SagiK-Repository/Balancer/docs/motor_test/test_1/motor_test_3_1749901958.csv

Time | Target0 | Target1 | Actual0 | Actual1 | Roll | Pitch | Confidence | Pos0 | Pos1
0.0002 | 10.0000 | 0.0000 | 14.9983 | -15.7754 | 0.0000 | 0.0000 | 0.0000 | 0.0012 | -0.0012
0.0200 | 10.0000 | 0.0000 | 14.9983 | -15.7754 | 0.0000 | 0.0000 | 0.0000 | 0.1001 | -0.1053
0.0411 | 10.0000 | 0.0000 | 14.9983 | -15.7754 | 0.0000 | 0.0000 | 0.0000 | 0.2057 | -0.2163
0.0611 | 10.0000 | 0.0000 | 14.9983 | -15.7754 | 0.0000 | 0.0000 | 0.0000 | 0.3054 | -0.3212
0.0811 | 10.0000 | 0.0000 | 14.9983 | -15.7754 | 0.0000 | 0.0000 | 0.0000 | 0.4054 | -0.4264
0.1011 | 10.0000 | 0.0000 | 14.9983 | -15.7754 | 0.0000 | 0.0000 | 0.0000 | 0.5054 | -0.5316
0.1211 | 10.0000 | 0.0000 | 14.9983 | -0.6457 | 0.0000 | 0.0000 | 0.0000 | 0.6054 | -0.0261
0.1413 | 10.0000 | 0.0000 | 14.9983 | -0.6457 | 0.0000 | 0.0000 | 0.0000 | 0.7067 | -0.0304
0.1611 | 10.0000 | 0.0000 | 14.9983 | -0.6457 | 0.0000 | 0.0000 | 0.0000 | 0.8053 | -0.0347
0.1811 | 10.0000 | 0.0000 | 14.9983 | -0.6457 | 0.0000 | 0.0000 | 0.0000 | 0.9053 | -0.0390
0.2011 | 10.0000 | 0.0000 | 14.9983 | -0.6457 | 0.0000 | 0.0000 | 0.0000 | 1.0052 | -0.0433
0.2211 | 10.0000 | 0.0000 | 14.9983 | -205.9349 | 0.0000 | 0.0000 | 0.0000 | 1.1053 | -15.1758
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
