SagiK-Repository/Balancer/docs/motor_test/test_1/motor_test_4_1749901995.csv

Time | Target0 | Target1 | Actual0 | Actual1 | Roll | Pitch | Confidence | Pos0 | Pos1
0.0001 | 1.0000 | 0.0000 | 14.9983 | 265.8498 | 0.0000 | 0.0000 | 0.0000 | 0.0005 | 0.0096
0.0206 | 1.0000 | 0.0000 | 14.9983 | 265.8498 | 0.0000 | 0.0000 | 0.0000 | 0.1032 | 1.8298
0.0411 | 1.0000 | 0.0000 | 14.9983 | 265.8498 | 0.0000 | 0.0000 | 0.0000 | 0.2054 | 3.6415
0.0611 | 1.0000 | 0.0000 | 14.9983 | 265.8498 | 0.0000 | 0.0000 | 0.0000 | 0.3054 | 5.4139
0.0811 | 1.0000 | 0.0000 | 14.9983 | 265.8498 | 0.0000 | 0.0000 | 0.0000 | 0.4054 | 7.1863
0.1011 | 1.0000 | 0.0000 | 14.9983 | 4.0456 | 0.0000 | 0.0000 | 0.0000 | 0.5054 | 0.1363
0.1211 | 1.0000 | 0.0000 | 14.9983 | 4.0456 | 0.0000 | 0.0000 | 0.0000 | 0.6054 | 0.1633
0.1411 | 1.0000 | 0.0000 | 14.9983 | 4.0456 | 0.0000 | 0.0000 | 0.0000 | 0.7054 | 0.1903
0.1611 | 1.0000 | 0.0000 | 14.9983 | 4.0456 | 0.0000 | 0.0000 | 0.0000 | 0.8054 | 0.2172
0.1811 | 1.0000 | 0.0000 | 14.9983 | 4.0456 | 0.0000 | 0.0000 | 0.0000 | 0.9054 | 0.2442
0.2011 | 1.0000 | 0.0000 | 14.9983 | 4.0456 | 0.0000 | 0.0000 | 0.0000 | 1.0054 | 0.2712
0.2211 | 1.0000 | 0.0000 | 14.9983 | 4.0456 | 0.0000 | 0.0000 | 0.0000 | 1.1054 | 0.2982
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
