SagiK-Repository/Balancer/docs/motor_test/test_1/motor_test_5_1749902016.csv

Time | Target0 | Target1 | Actual0 | Actual1 | Roll | Pitch | Confidence | Pos0 | Pos1
0.0001 | 0.0000 | 0.0000 | 14.9983 | -30.3309 | 0.0000 | 0.0000 | 0.0000 | 0.0005 | -0.0010
0.0200 | 0.0000 | 0.0000 | 14.9983 | -30.3309 | 0.0000 | 0.0000 | 0.0000 | 0.1002 | -0.2026
0.0411 | 0.0000 | 0.0000 | 14.9983 | -30.3309 | 0.0000 | 0.0000 | 0.0000 | 0.2054 | -0.4154
0.0611 | 0.0000 | 0.0000 | 14.9983 | -30.3309 | 0.0000 | 0.0000 | 0.0000 | 0.3054 | -0.6176
0.0811 | 0.0000 | 0.0000 | 14.9983 | -30.3309 | 0.0000 | 0.0000 | 0.0000 | 0.4054 | -0.8198
0.1011 | 0.0000 | 0.0000 | 14.9983 | -30.3309 | 0.0000 | 0.0000 | 0.0000 | 0.5054 | -1.0221
0.1211 | 0.0000 | 0.0000 | 14.9983 | -30.3309 | 0.0000 | 0.0000 | 0.0000 | 0.6054 | -1.2243
0.1411 | 0.0000 | 0.0000 | 14.9983 | -30.3309 | 0.0000 | 0.0000 | 0.0000 | 0.7054 | -1.4265
0.1611 | 0.0000 | 0.0000 | 14.9983 | -30.3309 | 0.0000 | 0.0000 | 0.0000 | 0.8054 | -1.6287
0.1811 | 0.0000 | 0.0000 | 14.9983 | -30.3309 | 0.0000 | 0.0000 | 0.0000 | 0.9053 | -1.8309
0.2011 | 0.0000 | 0.0000 | 14.9983 | -30.3309 | 0.0000 | 0.0000 | 0.0000 | 1.0053 | -2.0330
0.2211 | 0.0000 | 0.0000 | 14.9983 | -30.3309 | 0.0000 | 0.0000 | 0.0000 | 1.1053 | -2.2353
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
