SagiK-Repository/Balancer/docs/motor_test/test_2/motor_test_1_1749902902.csv

Time | Target0 | Target1 | Actual0 | Actual1 | Roll | Pitch | Confidence | Pos0 | Pos1
0.0004 | 0.0000 | 0.0000 | 14.8001 | 0.0000 | 0.1731 | -1.2958 | 99.4314 | 0.0018 | 0.0000
0.0200 | 0.0000 | 0.0000 | 14.8001 | 0.0000 | 0.1640 | -1.3071 | 99.6272 | 0.0985 | 0.0000
0.0410 | 0.0000 | 0.0000 | 14.8001 | 0.0000 | 0.1640 | -1.3071 | 99.6272 | 0.2024 | 0.0000
0.0610 | 0.0000 | 0.0000 | 14.8001 | 0.0000 | 0.1640 | -1.3071 | 99.6272 | 0.3011 | 0.0000
0.0810 | 0.0000 | 0.0000 | 14.8001 | 0.0000 | 0.1696 | -1.3116 | 100.0000 | 0.3997 | 0.0000
0.1010 | 0.0000 | 0.0000 | 14.8001 | 0.0000 | 0.1696 | -1.3116 | 100.0000 | 0.4984 | 0.0000
0.1210 | 0.0000 | 0.0000 | 14.8001 | 0.0000 | 0.1619 | -1.3049 | 95.5624 | 0.5971 | 0.0000
0.1410 | 0.0000 | 0.0000 | 14.8001 | 0.0000 | 0.1619 | -1.3049 | 95.5624 | 0.6957 | 0.0000
0.1610 | 0.0000 | 0.0000 | 14.8001 | 0.0000 | 0.1619 | -1.3049 | 95.5624 | 0.7944 | 0.0000
0.1810 | 0.0000 | 0.0000 | 14.8001 | 0.0000 | 0.1696 | -1.3234 | 96.4843 | 0.8931 | 0.0000
0.2010 | 0.0000 | 0.0000 | 14.8001 | 0.0000 | 0.1696 | -1.3234 | 96.4843 | 0.9917 | 0.0000
0.2210 | 0.0000 | 0.0000 | 14.8001 | 0.0000 | 0.1773 | -1.2996 | 99.9952 | 1.0904 | 0.0000
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
